penguin-awsome/Cashout-Station/Project Photos/Cashout Texturing.png

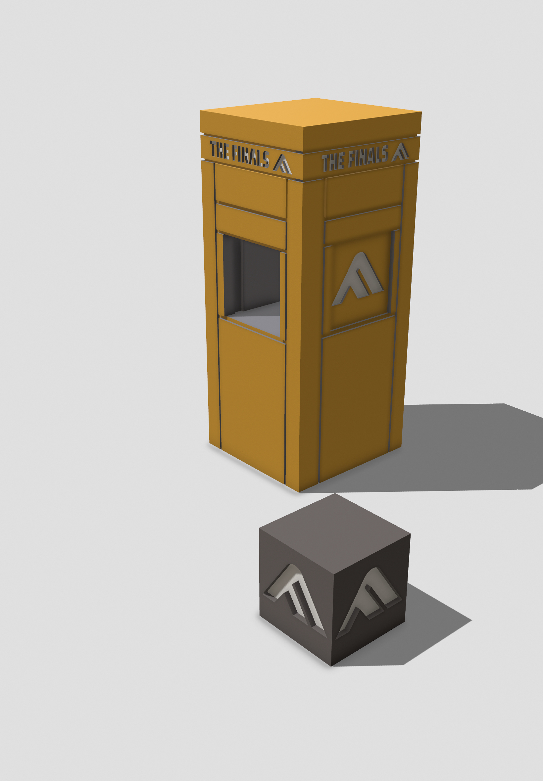
Project Photos/Cashout Texturing.png
