penguin-awsome/Cashout-Station/Project Photos/Good File Structure.png

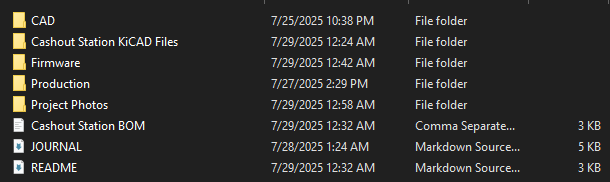
Project Photos/Good File Structure.png
