penguin-awsome/Cashout-Station/Project Photos/PCB Back Render.png

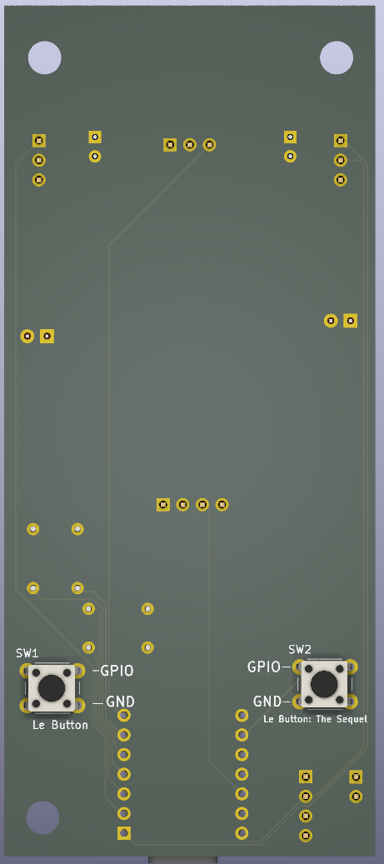
Project Photos/PCB Back Render.png
