penguin-awsome/Cashout-Station/Project Photos/PCB Front Render.png

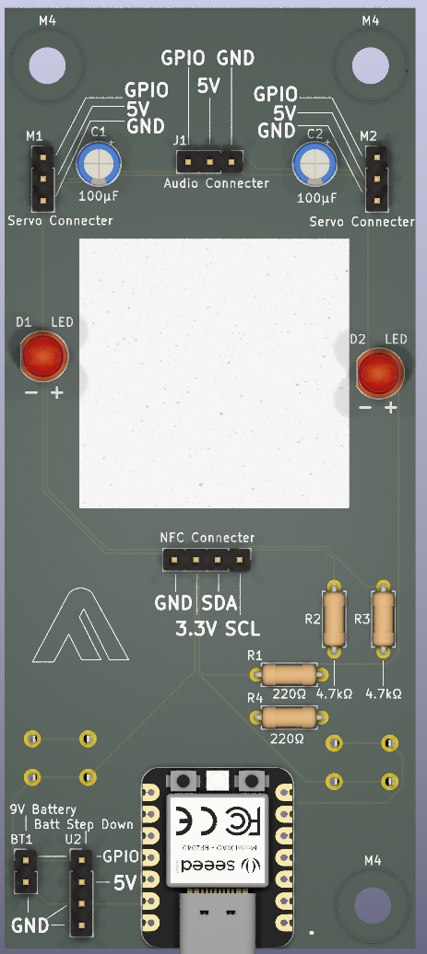
Project Photos/PCB Front Render.png
