penguin-awsome/Cashout-Station/Project Photos/Reciepts/Alibaba $4.90 USD.png

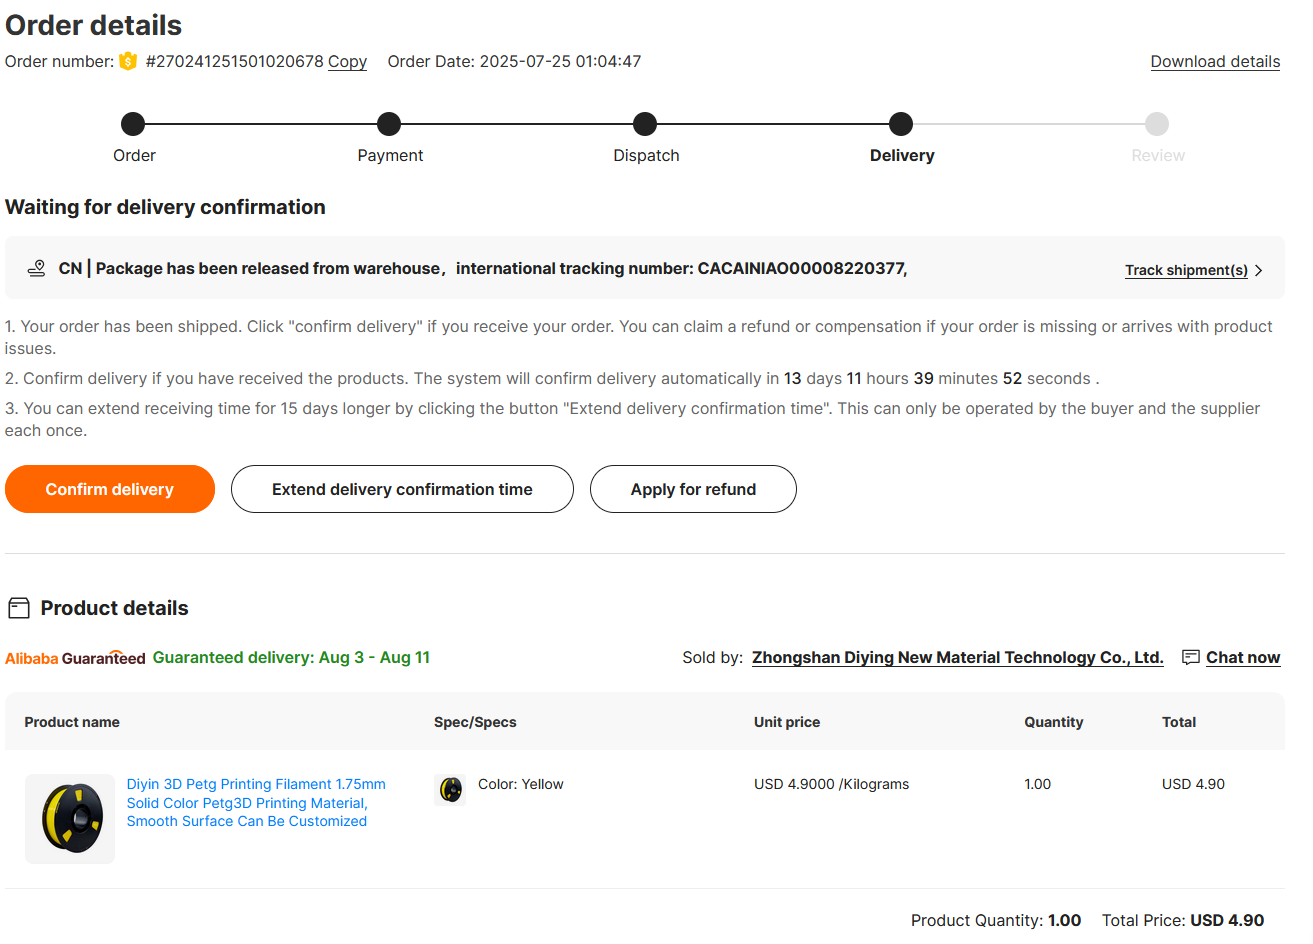
Project Photos/Reciepts/Alibaba $4.90 USD.png
