penguin-awsome/Cashout-Station/Project Photos/Reciepts/Aliepress $48.00 CAD.png

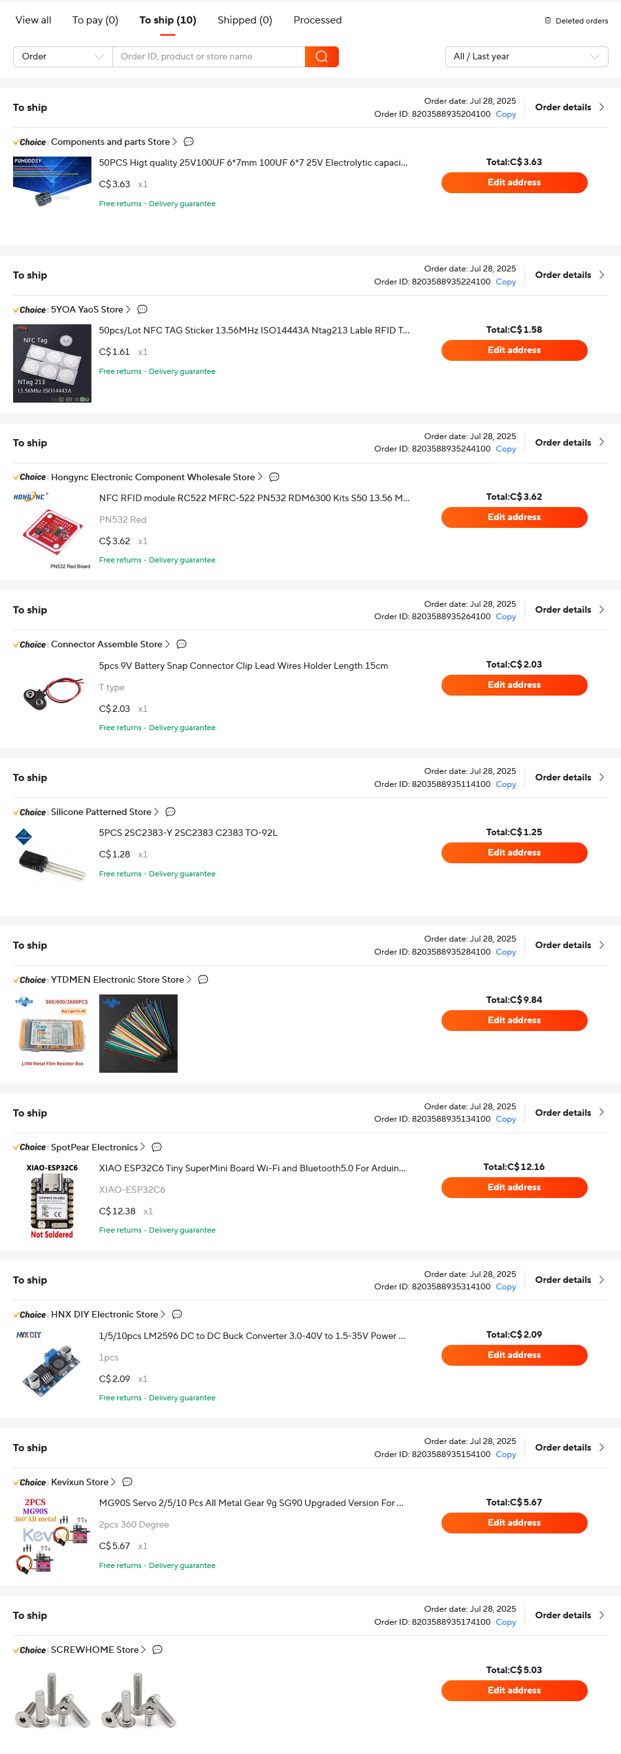
Project Photos/Reciepts/Aliepress $48.00 CAD.png
