penguin-awsome/Cashout-Station/Project Photos/Reciepts/Digikey $22.01 CAD.png

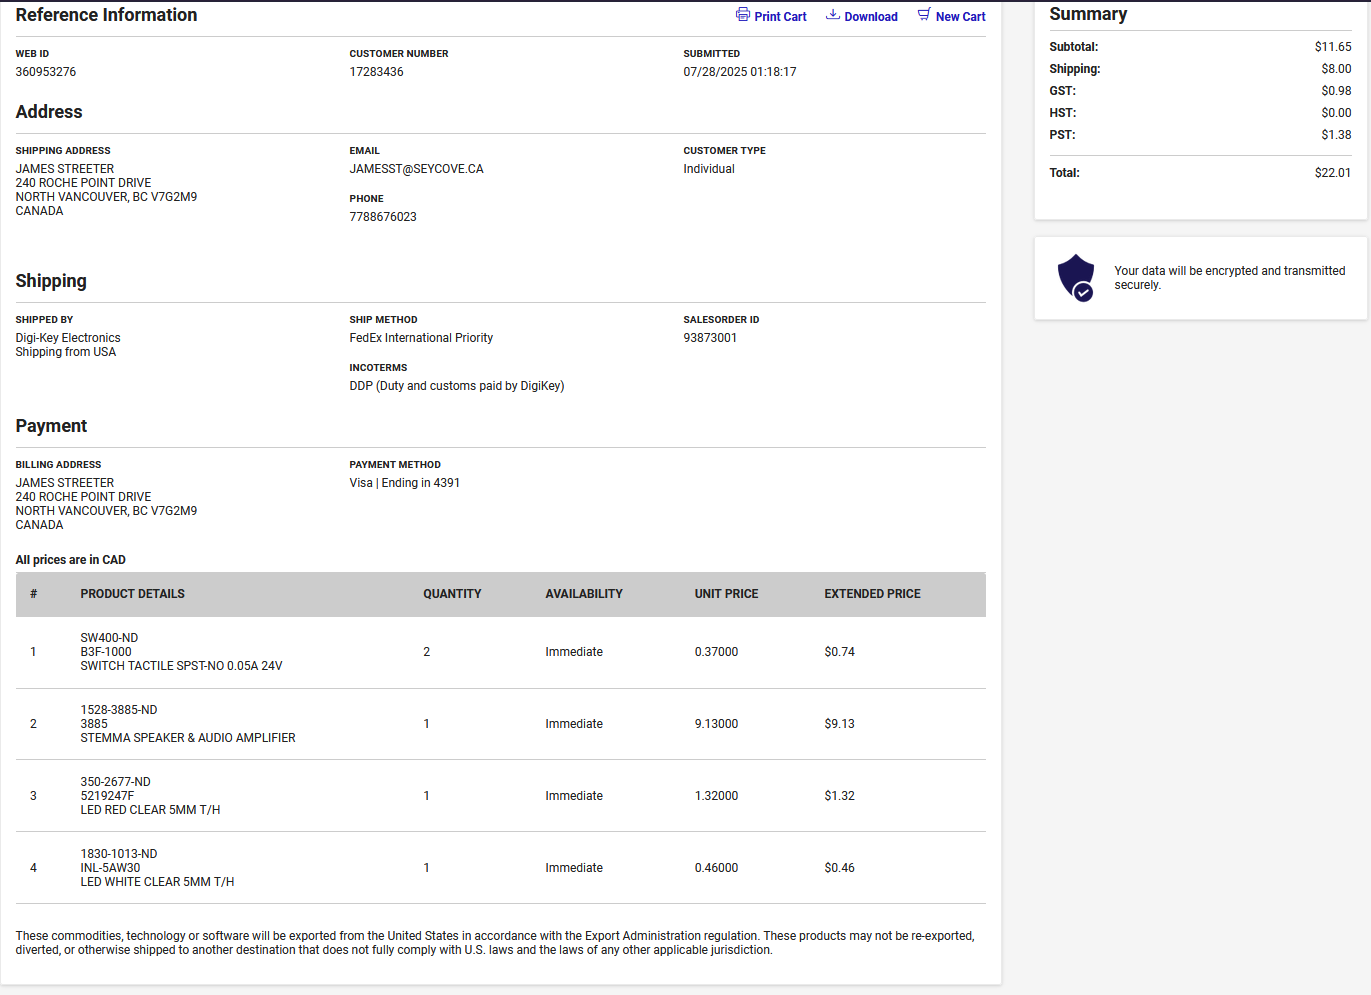
Project Photos/Reciepts/Digikey $22.01 CAD.png
