penguin-awsome/Cashout-Station/Project Photos/Reciepts/JLCPCB $6.00 CAD.png

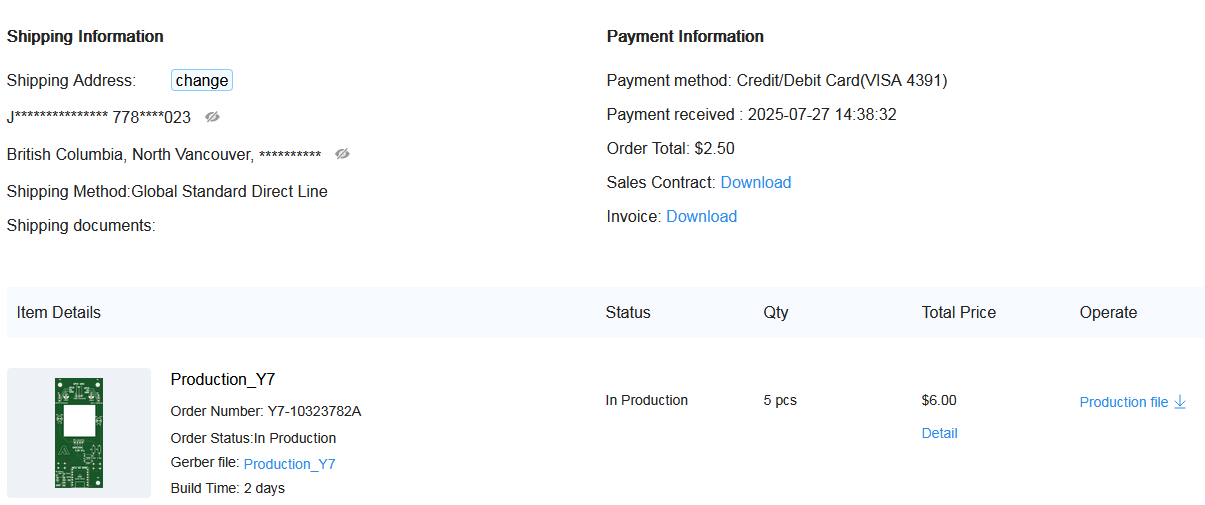
Project Photos/Reciepts/JLCPCB $6.00 CAD.png
