penguin-awsome/Cashout-Station/Project Photos/Cashout Component Layout.png

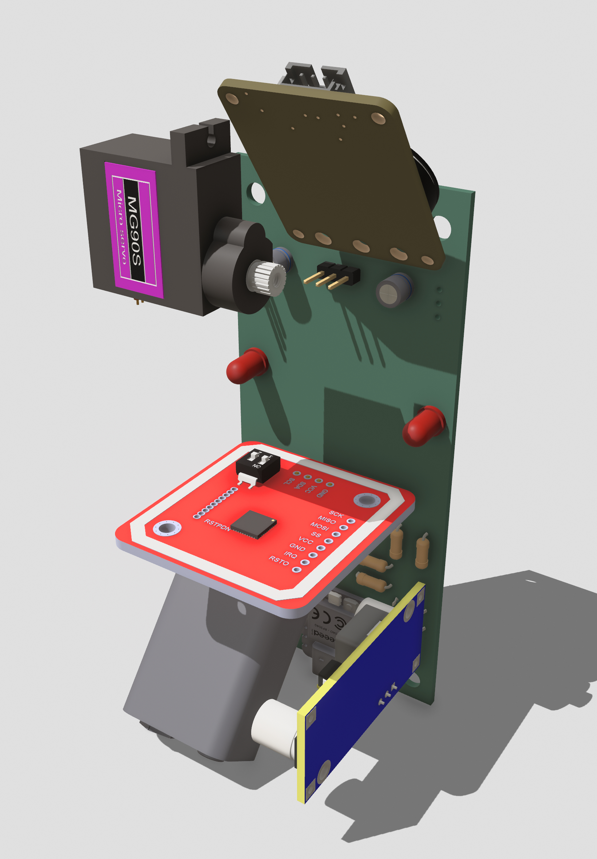
Project Photos/Cashout Component Layout.png
